Cloclo222/StringUs/Documents/Images/PA_window.jpg

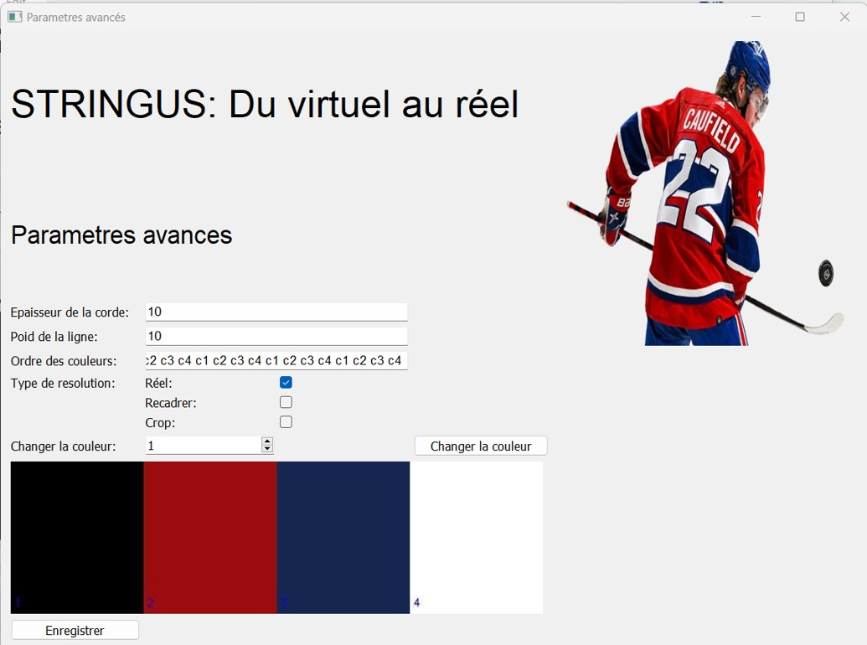
Documents/Images/PA_window.jpg
