Cloclo222/StringUs/Documents/Images/Progress_window.jpg

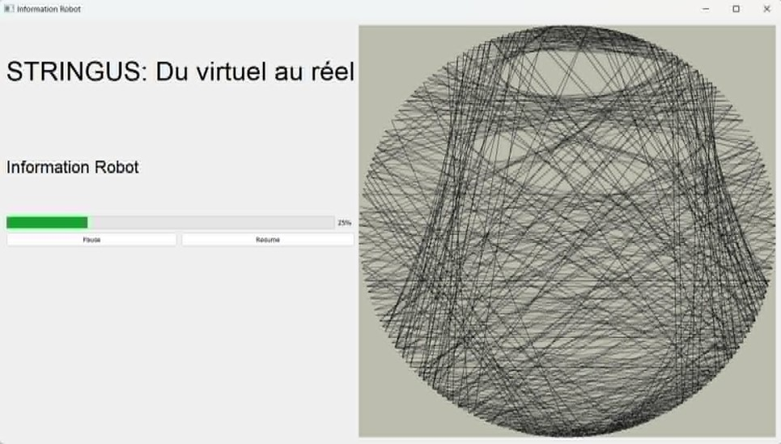
Documents/Images/Progress_window.jpg
