Cloclo222/StringUs/GUI/Input/no.png

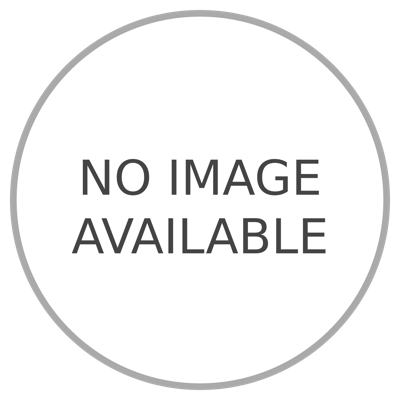
GUI/Input/no.png
