Cloclo222/StringUs/GUI/Input/work.png

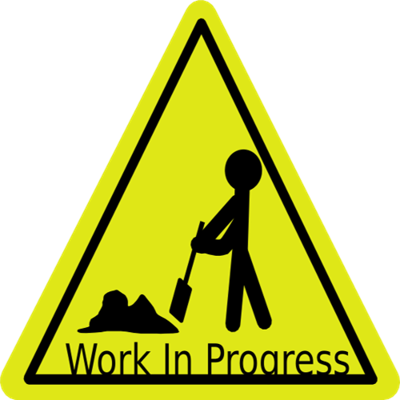
GUI/Input/work.png
