Cloclo222/StringUs/stringus_code_IDE/diagramme_communication.png

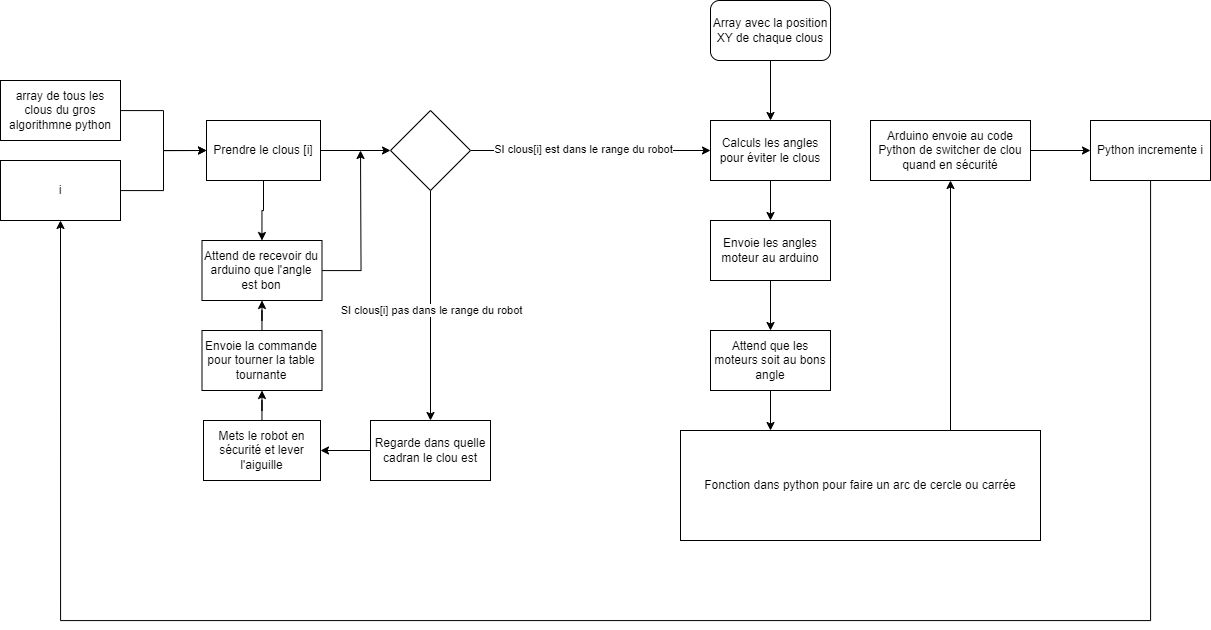
stringus_code_IDE/diagramme_communication.png
