Cloclo222/StringUs/Documents/Images/AssemblageStringUS.png

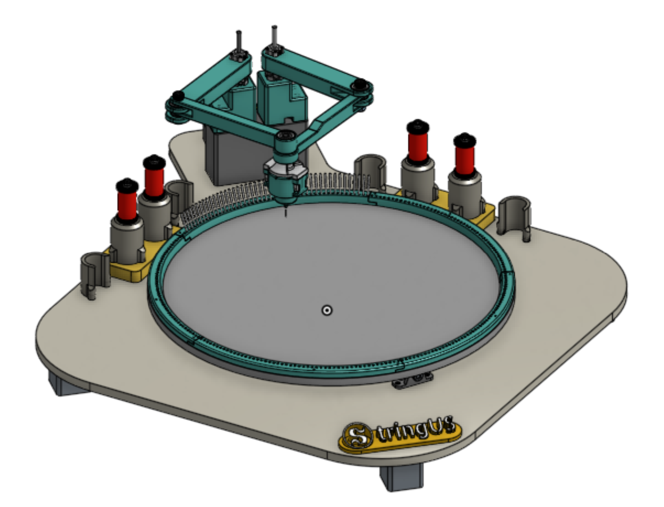
Documents/Images/AssemblageStringUS.png
