Cloclo222/StringUs/GUI/Window/PA_Window.py

import sys
import cv2
import csv
from PyQt5 import QtCore, QtGui, QtWidgets
from PyQt5.QtCore import *
import matplotlib
import numpy as np
from PyQt5.QtWidgets import *
from PyQt5.QtGui import *

from PyQt5.QtCore import (
    Qt, QObject, pyqtSignal, pyqtSlot, QRunnable, QThreadPool
)
from PyQt5 import QtCore as qtc

from PIL import Image
from .Crop_window1 import *


class Window_PA(QWidget):
    # Définition d'un signal émis lors de la soumission de paramètres
    submitted2 = qtc.pyqtSignal(list, str, int, int, str)

    def __init__(self, number_of_color_set: int, filename, rgb_image, pd, ep, seq, sizedef, grey):
        super().__init__()
        # Définition de la géométrie de la fenêtre
        self.setWindowTitle("Parametres avancés")
        self.setGeometry(100, 100, 500, 500)

        # Définition des éléments de l'interface utilisateur
        self.Titre = QLabel("STRINGUS: Du virtuel au réel")
        self.Titre.setFont(QFont('Arial', 30))

        self.sous_titre = QLabel("Parametres avances")
        self.sous_titre.setFont(QFont('Arial', 20))

        self.LargeurPhoto = QLabel("Largeur")
        self.LargeurPhoto.setFont(QFont('Arial', 9))

        self.HauteurPhoto = QLabel("Hauteur")
        self.HauteurPhoto.setFont(QFont('Arial', 9))

        self.CropButton = QPushButton("Crop l'image")
        self.CropButton.clicked.connect(self.isCropButtonPush)

        # Initialisation des variables avec les paramètres reçus
        self.nb_couleur = number_of_color_set
        self.real = filename
        self.size = sizedef
        self.Realrgb = rgb_image
        self.valueepaisseur = ep
        self.valueepaisseur = ep
        self.valuepoid = pd
        self.sequence = seq
        self.greyscale = grey
        self.temp = self.Realrgb.copy()
        self.image_a_imprimer = self.real

        self.EpaisseurLine = QLineEdit(str(ep))
        self.EpaisseurLine.setValidator(QIntValidator())
        self.EpaisseurLine.setMaxLength(4)
        self.EpaisseurLine.setAlignment(Qt.AlignLeft)
        self.EpaisseurLine.setFont(QFont("Arial", 10))

        self.PoidLine = QLineEdit(str(pd))
        self.PoidLine.setValidator(QIntValidator())
        self.PoidLine.setMaxLength(4)
        self.PoidLine.setAlignment(Qt.AlignLeft)
        self.PoidLine.setFont(QFont("Arial", 10))

        self.ResizeButton = QPushButton("Recadrer")
        self.ResizeButton.clicked.connect(self.isResizeButtonPush)

        self.LargeurPhotoLine = QLineEdit()
        self.LargeurPhotoLine.setValidator(QIntValidator())
        self.LargeurPhotoLine.setMaxLength(5)
        self.LargeurPhotoLine.setAlignment(Qt.AlignLeft)
        self.LargeurPhotoLine.setFont(QFont("Arial", 10))

        self.HauteurPhotoLine = QLineEdit()
        self.HauteurPhotoLine.setValidator(QIntValidator())
        self.HauteurPhotoLine.setMaxLength(5)
        self.HauteurPhotoLine.setAlignment(Qt.AlignLeft)
        self.HauteurPhotoLine.setFont(QFont("Arial", 10))

        if sizedef == "Real":
            self.Image = QLabel()
            self.pixmap = QPixmap(self.resize_image(400, 400, self.image_a_imprimer, 'Output/resize_image.png'))
            self.Image.setPixmap(self.pixmap)
        elif sizedef == "Resize":
            self.Image = QLabel()
            self.pixmap = QPixmap(self.image_a_imprimer)
            self.Image.setPixmap(self.pixmap)
        else:  # TEMPORAIRE
            self.Image = QLabel()
            self.pixmap = QPixmap(self.resize_image(400, 400, self.image_a_imprimer, 'Output/resize_image.png'))
            self.Image.setPixmap(self.pixmap)

        self.checkBox_Real = QCheckBox()
        self.checkBox_Real.setGeometry(qtc.QRect(170, 120, 81, 20))
        self.checkBox_Real.stateChanged.connect(self.checkeReal)

        self.checkBox_Resize = QCheckBox()
        self.checkBox_Resize.setGeometry(qtc.QRect(170, 120, 81, 20))
        self.checkBox_Resize.stateChanged.connect(self.checkeResize)

        self.checkBox_Crop = QCheckBox()
        self.checkBox_Crop.setGeometry(qtc.QRect(170, 120, 81, 20))
        self.checkBox_Crop.stateChanged.connect(self.checkCrop)

        self.CouleurChoiceBox = QSpinBox(minimum=1, maximum=self.nb_couleur, value=1)
        self.CouleurChoiceBox.valueChanged.connect(self.isCouleurChoiceBoxChange)

        self.DominantImage = QLabel()
        self.pixmap = QPixmap(
            self.resize_image(700, 200, 'Input/bar.jpg', 'Input/bar.jpg'))
        self.DominantImage.setPixmap(self.pixmap)

        self.OrdreLine = QLineEdit(seq)
        self.OrdreLine.setAlignment(Qt.AlignLeft)
        self.OrdreLine.setFont(QFont("Arial", 10))

        self.ChangeColorButton = QPushButton("Changer la couleur")
        self.ChangeColorButton.clicked.connect(self.isChangeColorButtonPush)

        self.SaveButton = QPushButton("Enregistrer")
        self.SaveButton.clicked.connect(self.SaveButtonPush)

        if self.greyscale:
            self.pixmap = QPixmap(
                self.resize_image(700, 200, 'Input/grey.jpg', 'Input/grey.jpg'))
            self.DominantImage.setPixmap(self.pixmap)
            self.ChangeColorButton.setHidden(True)
            self.OrdreLine.setHidden(True)

        layout = QGridLayout()

        # Ajout des widgets au layout
        layout.addWidget(self.Titre, 0, 0, 1, 4)
        layout.addWidget(self.sous_titre, 1, 0, 1, 4)
        layout.addWidget(self.Image, 0, 5, 4, 4)

        layout.addWidget(QLabel("Epaisseur de la corde:"), 2, 0, 1, 2)
        layout.addWidget(self.EpaisseurLine, 2, 1, 1, 2)
        layout.addWidget(QLabel("Poid de la ligne:"), 3, 0, 1, 2)
        layout.addWidget(self.PoidLine, 3, 1, 1, 2)
        layout.addWidget(QLabel("Ordre des couleurs:"), 4, 0, 1, 2)
        layout.addWidget(self.OrdreLine, 4, 1, 1, 2)

        layout.addWidget(QLabel("Type de resolution:"), 5, 0)
        layout.addWidget(QLabel("Réel:"), 5, 1)
        layout.addWidget(self.checkBox_Real, 5, 2)
        layout.addWidget(self.LargeurPhoto, 6, 6)
        layout.addWidget(self.HauteurPhoto, 6, 7)
        layout.addWidget(self.LargeurPhotoLine, 7, 6)
        layout.addWidget(self.HauteurPhotoLine, 7, 7)
        layout.addWidget(self.ResizeButton, 8, 6)

        layout.addWidget(QLabel("Recadrer:"), 6, 1)
        layout.addWidget(self.checkBox_Resize, 6, 2)
        layout.addWidget(QLabel("Crop:"), 7, 1)
        layout.addWidget(self.checkBox_Crop, 7, 2)

        layout.addWidget(QLabel("Changer la couleur:"), 8, 0)
        layout.addWidget(self.CouleurChoiceBox, 8, 1)
        layout.addWidget(self.ChangeColorButton, 8, 3, 1, 2)

        layout.addWidget(self.CropButton, 4, 5, 3, 4)
        layout.addWidget(self.DominantImage, 9, 0, 1, 4)
        layout.addWidget(self.SaveButton, 10, 0, 1, 1)

        if self.size == "Real":
            self.checkBox_Resize.setChecked(False)
            self.checkBox_Crop.setChecked(False)
            self.checkBox_Real.setChecked(True)
        elif self.size == "Resize":
            self.checkBox_Resize.setChecked(True)
            self.checkBox_Real.setChecked(False)
            self.checkBox_Crop.setChecked(False)
            self.LargeurPhotoLine.setHidden(False)
            self.HauteurPhotoLine.setHidden(False)
            self.LargeurPhoto.setHidden(False)
            self.HauteurPhoto.setHidden(False)
            self.ResizeButton.setHidden(False)
        else:
            self.checkBox_Resize.setChecked(False)
            self.checkBox_Real.setChecked(False)
            self.checkBox_Crop.setChecked(True)
            self.CropButton.setHidden(False)

        self.setLayout(layout)

    def checkCrop(self):
        # Cette méthode est appelée lorsque la case à cocher "Crop" est activée ou désactivée
        if self.checkBox_Crop.checkState():
            # Met à jour la variable size pour indiquer le mode "Crop"
            self.size = "Crop"
            # Désactive les autres cases à cocher
            self.checkBox_Resize.setChecked(False)
            self.checkBox_Real.setChecked(False)
            # Cache les éléments liés au redimensionnement
            self.LargeurPhotoLine.setHidden(True)
            self.HauteurPhotoLine.setHidden(True)
            self.LargeurPhoto.setHidden(True)
            self.HauteurPhoto.setHidden(True)
            self.ResizeButton.setHidden(True)
            # Affiche le bouton de recadrage
            self.CropButton.setHidden(False)

    def checkeReal(self):
        # Cette méthode est appelée lorsque la case à cocher "Real" est activée ou désactivée
        if self.checkBox_Real.checkState():
            # Met à jour la variable size pour indiquer le mode "Real"
            self.size = "Real"
            # Désactive les autres cases à cocher
            self.checkBox_Resize.setChecked(False)
            self.checkBox_Crop.setChecked(False)
            # Cache les éléments liés au redimensionnement
            self.LargeurPhotoLine.setHidden(True)
            self.HauteurPhotoLine.setHidden(True)
            self.LargeurPhoto.setHidden(True)
            self.HauteurPhoto.setHidden(True)
            self.ResizeButton.setHidden(True)
            # Cache le bouton de recadrage
            self.CropButton.setHidden(True)
            # Met à jour l'image affichée avec l'image réelle
            self.image_a_imprimer = self.real
            self.pixmap = QPixmap(self.resize_image(400, 400, self.image_a_imprimer, 'Output/resize_image.png'))
            self.Image.setPixmap(self.pixmap)

    def checkeResize(self):
        # Cette méthode est appelée lorsque la case à cocher "Resize" est activée ou désactivée
        if self.checkBox_Resize.checkState():
            # Met à jour la variable size pour indiquer le mode "Resize"
            self.size = "Resize"
            # Désactive les autres cases à cocher
            self.checkBox_Real.setChecked(False)
            self.checkBox_Crop.setChecked(False)
            # Affiche les éléments liés au redimensionnement
            self.LargeurPhotoLine.setHidden(False)
            self.HauteurPhotoLine.setHidden(False)
            self.LargeurPhoto.setHidden(False)
            self.HauteurPhoto.setHidden(False)
            # Cache le bouton de recadrage et affiche le bouton de redimensionnement
            self.CropButton.setHidden(True)
            self.ResizeButton.setHidden(False)
            print("Resize")

    def isCouleurChoiceBoxChange(self):
        # Cette méthode est appelée lorsqu'une nouvelle couleur est sélectionnée
        self.numero_de_couleur = self.CouleurChoiceBox.value()
        return

    def isResizeButtonPush(self):
        # Cette méthode est appelée lorsque le bouton de redimensionnement est cliqué
        # Récupère la largeur et la hauteur saisies par l'utilisateur
        largeur = int(self.LargeurPhotoLine.text())
        hauteur = int(self.HauteurPhotoLine.text())
        # Redimensionne l'image et met à jour l'affichage
        self.image_a_imprimer = self.resize_image(largeur, hauteur, self.image_a_imprimer, 'Output/BoxResize.png')
        self.pixmap = QPixmap(self.image_a_imprimer)
        self.Image.setPixmap(self.pixmap)

    def isChangeColorButtonPush(self):
        # Cette méthode est appelée lorsque le bouton pour changer la couleur est cliqué
        self.isCouleurChoiceBoxChange()
        # Affiche la boîte de dialogue pour choisir une nouvelle couleur
        color = QColorDialog.getColor()
        if color.isValid():
            # Met à jour la couleur sélectionnée dans la liste des couleurs
            NewRGB = color.getRgb()
            NewRGB = NewRGB[0:3]
            indice = self.numero_de_couleur - 1
            indice = int(indice)
            self.temp[indice] = NewRGB
            self.redoBand(self.temp)
            self.pixmap = QPixmap(self.resize_image(700, 200, 'Input/bar.jpg', 'Input/bar.jpg'))
            self.DominantImage.setPixmap(self.pixmap)

    def SaveButtonPush(self):
        # Cette méthode est appelée lorsque le bouton d'enregistrement est cliqué
        if self.checkBox_Resize.checkState() == False and self.checkBox_Real.checkState() == False and self.checkBox_Crop.checkState() == False:
            # Affiche un message d'erreur si aucun mode n'est sélectionné
            QMessageBox.information(self, 'ERREUR', "Il n'y a pas de type de resolution coche (;", QMessageBox.Ok)
            return
        else:
            # Met à jour les paramètres avec les valeurs actuelles et émet le signal
            self.Realrgb = self.temp
            self.valuepoid = int(self.PoidLine.text())
            self.valueepaisseur = int(self.EpaisseurLine.text())
            self.sequence = self.OrdreLine.text()
            self.submitted2.emit(self.Realrgb, self.size, self.valueepaisseur, self.valuepoid, self.sequence)
            self.close()

    def isCropButtonPush(self):
        # Cette méthode est appelée lorsque le bouton de recadrage est cliqué
        # lol = ['Output/resize_image.png']
        # self.window = Crop(lol)
        # self.window.show()
        dlg = QMessageBox(self)
        dlg.setWindowTitle("oops")
        dlg.setText("Crop feature not yet implemented :(")
        button = dlg.exec()
        if button == QMessageBox.Ok:
            dlg.close()

    def resize_image(self, largeur, hauteur, image_path, save_as):
        # Cette méthode redimensionne une image et la sauvegarde
        image = Image.open(image_path)
        resized = image.resize((largeur, hauteur))
        resized.save(save_as)
        return save_as

    def redoBand(self, new_rgb):
        # Cette méthode recrée les barres de couleur dominante
        font = cv2.FONT_HERSHEY_SIMPLEX
        bars = []
        onessaye = []
        for index, row in enumerate(new_rgb):
            bar, rgb = self.create_bar(200, 200, row)
            bars.append(bar)
            onessaye.append(rgb)
        img_bar = np.hstack(bars)
        for index, row in enumerate(onessaye):
            image = cv2.putText(img_bar, f'{index + 1}', (5 + 200 * index, 200 - 10),
                                font, 0.5, (255, 0, 0), 1, cv2.LINE_AA)
        cv2.imwrite('Input/bar.jpg', img_bar)
        cv2.waitKey(0)

    def create_bar(self, height, width, color):
        # Cette méthode crée une barre de couleur
        bar = np.zeros((height, width, 3), np.uint8)
        red, green, blue = int(color[0]), int(color[1]), int(color[2])
        bar[:] = (blue, green, red)
        return bar, (red, green, blue)
